Angelussss/Ducker-Charger/firmware/emulator/emu_config.ini

# Ducker-Charger PCB emulator — board & scenario configuration
# Read at startup; edit and relaunch, no rebuild needed.

# battery
soc = 87               # initial state of charge, %
soh = 97                # state of health, %
cycles = 42
ambient_c = 25
time_scale = 60         # battery time acceleration (60 = 1 min -> 1 h)
quiescent_ma = 30       # board idle draw from the pack

# C1 charger (TPS25750 side) PD contract offered when plugged
charge_ma = 3000        # CC charge current into the pack
c1_mv = 20000
c1_ma = 3000

# C1 as source (key 'd': sink device attached, powerbank powers it)
# 20 V / 3 A: BQ25713 OTG boost reaches ~20.8 V max, so a 20 V PDO is
# the top of what the real hardware can advertise
c1src_mv = 20000
c1src_ma = 5000

# C2 sink (CYPD3175 side) contract requested when a device attaches
c2_mv = 15000
c2_ma = 3000

# USB-A loads (drawn when attached with key 1 / 2 and port enabled)
a1_load_ma = 3000
a2_load_ma = 3000

# Bench load on the lab output (key l). Resistive: draws Vout / R, clamped
# by the STPD01 ILIM programmed from the OUTPUT page.
lab_load_ohm = 2.5

# IC behavior
tps_app_mode = 0        # 0 = boot in PTCH mode (exercise the patch flow)
tps_strict_len = 1      # 1 = faithful TPS25750 length-prefixed protocol
                        # (charge.c framing bug fixed — keep 1)
gauge_provisioned = 0   # 0 = blank data flash (exercise provisioning.c)
bckl_active_low = 1     # JP402 jumper: 1 = PMOS (faithful to ili9341.c).
                        # fsm.c now drives the pin through ILI9341_Backlight,
                        # so polarity is consistent everywhere (finding #6 fixed)
