Angelussss/Ducker-Charger/firmware/cubeMX/Core/Src/display/gfx.c

/**
 * @file    gfx.c
 * @brief   pixel tools: font, lines, rects, scaled text, bitmap blit.
 */

#include "display/gfx.h"
#include <stdio.h>    /* snprintf */
#include <string.h>   /* strlen   */

/* =========================================================
 * BITMAP FONT DATA – Small 6x8
 *
 * Covers ASCII characters 32 (' ') through 122 ('z').
 * Contains: digits (48–57), uppercase (65–90), lowercase (97–122)
 * and common punctuation. Sufficient for the project UI.
 * For a complete font a library such as u8g2 can be used.
 * ========================================================= */
static const uint8_t _font_small_data[] = {
    /* Chars 32–47 – space and basic punctuation / Spazio e punteggiatura base */
    0x00,0x00,0x00,0x00,0x00,0x00,0x00,0x00,  /* ' ' (32) */
    0x00,0x00,0x5F,0x00,0x00,0x00,0x00,0x00,  /* '!' (33) */
    0x00,0x07,0x00,0x07,0x00,0x00,0x00,0x00,  /* '"' (34) */
    0x14,0x7F,0x14,0x7F,0x14,0x00,0x00,0x00,  /* '#' (35) */
    0x24,0x2A,0x7F,0x2A,0x12,0x00,0x00,0x00,  /* '$' (36) */
    0x23,0x13,0x08,0x64,0x62,0x00,0x00,0x00,  /* '%' (37) */
    0x36,0x49,0x55,0x22,0x50,0x00,0x00,0x00,  /* '&' (38) */
    0x00,0x05,0x03,0x00,0x00,0x00,0x00,0x00,  /* ''' (39) */
    0x00,0x1C,0x22,0x41,0x00,0x00,0x00,0x00,  /* '(' (40) */
    0x00,0x41,0x22,0x1C,0x00,0x00,0x00,0x00,  /* ')' (41) */
    0x0A,0x04,0x1F,0x04,0x0A,0x00,0x00,0x00,  /* '*' (42) */
    0x08,0x08,0x3E,0x08,0x08,0x00,0x00,0x00,  /* '+' (43) */
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
    0x7C,0x08,0x04,0x04,0x78,0x00,0x00,0x00,  /* 'n' (110) */
    0x38,0x44,0x44,0x44,0x38,0x00,0x00,0x00,  /* 'o' (111) */
    0x7C,0x14,0x14,0x14,0x08,0x00,0x00,0x00,  /* 'p' (112) */
    0x08,0x14,0x14,0x18,0x7C,0x00,0x00,0x00,  /* 'q' (113) */
    0x7C,0x08,0x04,0x04,0x08,0x00,0x00,0x00,  /* 'r' (114) */
    0x48,0x54,0x54,0x54,0x20,0x00,0x00,0x00,  /* 's' (115) */
    0x04,0x3F,0x44,0x40,0x20,0x00,0x00,0x00,  /* 't' (116) */
    0x3C,0x40,0x40,0x20,0x7C,0x00,0x00,0x00,  /* 'u' (117) */
    0x1C,0x20,0x40,0x20,0x1C,0x00,0x00,0x00,  /* 'v' (118) */
    0x3C,0x40,0x30,0x40,0x3C,0x00,0x00,0x00,  /* 'w' (119) */
    0x44,0x28,0x10,0x28,0x44,0x00,0x00,0x00,  /* 'x' (120) */
    0x0C,0x50,0x50,0x50,0x3C,0x00,0x00,0x00,  /* 'y' (121) */
    0x44,0x64,0x54,0x4C,0x44,0x00,0x00,0x00,  /* 'z' (122) */
};

/* =========================================================
 * PUBLIC FONT DESCRIPTORS
 *
 * FontMedium and FontLarge use the same data as a placeholder.
 * They should be replaced with proper larger font arrays when
 * the display hardware is available for testing.
 * ========================================================= */
const GFX_Font_t GFX_FontSmall  = { _font_small_data, 6, 8  };
const GFX_Font_t GFX_FontMedium = { _font_small_data, 6, 8  }; /* placeholder */
const GFX_Font_t GFX_FontLarge  = { _font_small_data, 6, 8  }; /* placeholder */

/* =========================================================
 * IMPLEMENTATION
 * ========================================================= */

void GFX_DrawChar(uint16_t x, uint16_t y, char c,
                  const GFX_Font_t *font, uint16_t fg_color, uint16_t bg_color)
{
    /* glyph not in font: skip quiet */
    if (c < 32 || c > 122) return;

    uint8_t char_index = (uint8_t)c - 32;
    const uint8_t *char_data = &font->data[char_index * font->char_h];

    /* font data column-major (font5x7 way): one byte = one column,
     * bit 0 = top pixel. old code read it row-major, text came out
     * alien. do not do that again. */
    for (uint8_t col = 0; col < font->char_w; col++)
    {
        uint8_t col_data = char_data[col];
        for (uint8_t row = 0; row < font->char_h; row++)
        {
            uint16_t color = (col_data & (1u << row)) ? fg_color : bg_color;
            ILI9341_DrawPixel(x + col, y + row, color);
        }
    }
}

static void draw_char_scaled(uint16_t x, uint16_t y, char c,
                             const GFX_Font_t *font, uint8_t scale,
                             uint16_t fg_color, uint16_t bg_color)
{
    if (c < 32 || c > 122) return;
    const uint8_t *char_data = &font->data[((uint8_t)c - 32) * font->char_h];

    for (uint8_t col = 0; col < font->char_w; col++)
    {
        uint8_t col_data = char_data[col];
        for (uint8_t row = 0; row < font->char_h; row++)
        {
            uint16_t color = (col_data & (1u << row)) ? fg_color : bg_color;
            ILI9341_FillRect(x + col * scale, y + row * scale, scale, scale, color);
        }
    }
}

void GFX_DrawStringScaled(uint16_t x, uint16_t y, const char *str,
                          const GFX_Font_t *font, uint8_t scale,
                          uint16_t fg_color, uint16_t bg_color)
{
    if (str == NULL || scale == 0) return;
    uint16_t cx = x;
    while (*str) {
        draw_char_scaled(cx, y, *str++, font, scale, fg_color, bg_color);
        cx += (font->char_w + 1) * scale;
    }
}

void GFX_DrawBitmap(uint16_t x, uint16_t y, uint16_t w, uint16_t h,
                    const uint16_t *data)
{
    for (uint16_t j = 0; j < h; j++)
        for (uint16_t i2 = 0; i2 < w; i2++)
            ILI9341_DrawPixel(x + i2, y + j, data[j * w + i2]);
}

void GFX_DrawString(uint16_t x, uint16_t y, const char *str,
                    const GFX_Font_t *font, uint16_t fg_color, uint16_t bg_color)
{
    if (str == NULL) return;

    uint16_t cursor_x = x;
    while (*str)
    {
        GFX_DrawChar(cursor_x, y, *str, font, fg_color, bg_color);
        cursor_x += font->char_w;
        str++;
    }
}

void GFX_DrawInt(uint16_t x, uint16_t y, int32_t value,
                 const GFX_Font_t *font, uint16_t fg_color, uint16_t bg_color)
{
    char buf[16];
    snprintf(buf, sizeof(buf), "%ld", (long)value);
    GFX_DrawString(x, y, buf, font, fg_color, bg_color);
}

void GFX_DrawHLine(uint16_t x, uint16_t y, uint16_t w, uint16_t color)
{
    /* A horizontal line is just a 1-pixel-tall rectangle. */
    ILI9341_FillRect(x, y, w, 1, color);
}

void GFX_DrawVLine(uint16_t x, uint16_t y, uint16_t h, uint16_t color)
{
    /* A vertical line is a 1-pixel-wide rectangle. */
    ILI9341_FillRect(x, y, 1, h, color);
}

void GFX_DrawRect(uint16_t x, uint16_t y, uint16_t w, uint16_t h, uint16_t color)
{
    GFX_DrawHLine(x,         y,         w, color);  /* top    / lato superiore */
    GFX_DrawHLine(x,         y + h - 1, w, color);  /* bottom / lato inferiore */
    GFX_DrawVLine(x,         y,         h, color);  /* left   / lato sinistro  */
    GFX_DrawVLine(x + w - 1, y,         h, color);  /* right  / lato destro    */
}

void GFX_DrawLine(uint16_t x0, uint16_t y0, uint16_t x1, uint16_t y1, uint16_t color)
{
    /* Bresenham's line algorithm.
     * This is the standard algorithm for rasterising a line on a pixel display
     * because it uses only integer additions and subtractions (no floating point). */
    int16_t dx =  (int16_t)(x1 > x0 ? x1 - x0 : x0 - x1);
    int16_t dy = -(int16_t)(y1 > y0 ? y1 - y0 : y0 - y1);
    int16_t sx = (x0 < x1) ? 1 : -1;
    int16_t sy = (y0 < y1) ? 1 : -1;
    int16_t err = dx + dy;

    while (1)
    {
        ILI9341_DrawPixel(x0, y0, color);
        if (x0 == x1 && y0 == y1) break;
        int16_t e2 = 2 * err;
        if (e2 >= dy) { err += dy; x0 = (uint16_t)((int16_t)x0 + sx); }
        if (e2 <= dx) { err += dx; y0 = (uint16_t)((int16_t)y0 + sy); }
    }
}

void GFX_DrawRoundRect(uint16_t x, uint16_t y, uint16_t w, uint16_t h,
                       uint16_t r, uint16_t color)
{
    /* Straight sides */
    GFX_DrawHLine(x + r,     y,         w - 2*r, color); /* top    */
    GFX_DrawHLine(x + r,     y + h - 1, w - 2*r, color); /* bottom */
    GFX_DrawVLine(x,         y + r,     h - 2*r, color); /* left   */
    GFX_DrawVLine(x + w - 1, y + r,     h - 2*r, color); /* right  */
    /* TODO: add corner arcs once display hardware is available for testing. */
}

void GFX_FillRoundRect(uint16_t x, uint16_t y, uint16_t w, uint16_t h,
                       uint16_t r, uint16_t color)
{
    /* Central body + top and bottom strips */
    ILI9341_FillRect(x,     y + r,     w,       h - 2*r, color);
    ILI9341_FillRect(x + r, y,         w - 2*r, r,       color);
    ILI9341_FillRect(x + r, y + h - r, w - 2*r, r,       color);
    /* TODO: fill corner arcs */
}

void GFX_DrawCircle(uint16_t cx, uint16_t cy, uint16_t r, uint16_t color)
{
    /* Midpoint circle algorithm (Bresenham for circles).
     * Thanks to 8-fold symmetry, we compute only 1/8 of the circle and
     * mirror it onto the other 7 octants. */
    int16_t x = 0, y = (int16_t)r, d = (int16_t)(3 - 2*r);

    while (x <= y)
    {
        /* 8-fold symmetry: plot all octants */
        ILI9341_DrawPixel(cx + (uint16_t)x, cy + (uint16_t)y, color);
        ILI9341_DrawPixel(cx - (uint16_t)x, cy + (uint16_t)y, color);
        ILI9341_DrawPixel(cx + (uint16_t)x, cy - (uint16_t)y, color);
        ILI9341_DrawPixel(cx - (uint16_t)x, cy - (uint16_t)y, color);
        ILI9341_DrawPixel(cx + (uint16_t)y, cy + (uint16_t)x, color);
        ILI9341_DrawPixel(cx - (uint16_t)y, cy + (uint16_t)x, color);
        ILI9341_DrawPixel(cx + (uint16_t)y, cy - (uint16_t)x, color);
        ILI9341_DrawPixel(cx - (uint16_t)y, cy - (uint16_t)x, color);
        if (d < 0) { d += 4*x + 6; }
        else       { d += 4*(x - y) + 10; y--; }
        x++;
    }
}
